Viva-la-Insomnia/OSHW-Smartwatch/Simplicity_project/inc/LS013_MD.h

/**************************************************************************//**
 * @file LS013_MD.c
 * @brief LS013B4DN04 interface code header
 * @author Tuomas Tinus, Jimi Järvelin
 * @version 0.5
 ******************************************************************************/

#ifndef __EM_SYSTEM_H
#define __EM_SYSTEM_H
#endif

#ifndef __EM_DEVICE_H
#define __EM_DEVICE_H
#endif

#ifndef __EM_CHIP_H
#define __EM_CHIP_H
#endif

#ifndef __EM_GPIO_H
#define __EM_GPIO_H
#endif

#ifndef __EM_USART_H
#define __EM_USART_H
#endif

#ifndef __UDELAY_H
#define __UDELAY_H
#endif

#ifndef __MATH_H
#define __MATH_H
#endif

#ifndef __STDINT_H
#define __STDINT_H
#endif

#ifndef __STRING_H
#define __STRING_H
#endif

typedef struct SpriteType {

	uint8_t WIDTH, HEIGHT;
	uint16_t* SPRITE;

	/* Sprite file to draw on the display
	 * Actual sprite consists of an array of pixels in uint16_t with inverse bit order (because comms are LSB-first
	 * and images are MSB-first)
	 * Sprite that is not 16n pixels wide has leading zeros added in the beginning of every line
	 * HEIGHT and WIDTH are measured in bits
	 * */

} Sprite;

typedef struct SpriteType Sprite;

void LS013_InvertBuffer(void); //Internal
void LS013_DispSpiTransmit (uint16_t* data, unsigned int len); //Internal
void LS013_DrawLines( uint8_t start_column, uint8_t width, uint16_t* data ); //Internal
void LS013_Init(void);
void LS013_Refresh( bool whole_display ); /*Refreshes the display, sending in the framebuffer.
whole_display forces a complete display refresh. !Automatically puts the display to dynamic mode! */
void LS013_ClearBufferArea( uint32_t xstart, uint32_t ystart, uint32_t xwidth, uint32_t ywidth, int color );
//Clears the framebuffer area
void LS013_DrawSprite( uint32_t posx, uint32_t posy, const Sprite sprite );
/* Draws a Sprite object on the display framebuffer. merge_draw merges the sprite with existing framebuffer image
instead of overwriting it																						*/
void LS013_SetBuffer( const uint16_t* img ); //Copies a display-sized image to display framebuffer
void LS013_ClearBuffer(void); //Clears the display framebuffer
void LS013_InvertPolarity(void); //Has to be called at least once per second (see datasheet of display)
void LS013_StaticMode(void); // Puts the display to static mode which saves power
void LS013_Enable(void); //Turns on the display driver
void LS013_Disable(void); //Shuts display down completely
