Viva-la-Insomnia/OSHW-Smartwatch/Simplicity_project/inc/Graphics.h

/**************************************************************************//**
 * @file Graphics.h
 * @brief Graphic file header
 * @author Tuomas Tinus, Jimi Järvelin
 * @version 0.5
 ******************************************************************************/

#ifndef GRAPHICS_H_
#define GRAPHICS_H_
#endif

extern const uint16_t LoadingBackground[]; //A neat picture of a stormtrooper
