Viva-la-Insomnia/OSHW-Smartwatch/Simplicity_project/inc/mdelay.h

/**************************************************************************//**
 * @file mdelay.h
 * @brief Microsecond delay header
 * @author Tuomas Tinus, Jimi Järvelin
 * @version 0.5
 ******************************************************************************/
void MDELAY_Delay(uint8_t microseconds);
