Viva-la-Insomnia/OSHW-Smartwatch/Simplicity_project/inc/udelay.h

/**************************************************************************//**
 * @file udelay.h
 ******************************************************************************/

void UDELAY_Calibrate(void);
void UDELAY_Delay( uint32_t usecs );
